shannon-greenlight/bonkulator/code/Bonkulator/trigger_fxns.h

// Trigger functions
#include "Arduino.h"

void clear_trigger(int output_num, int trig_num)
{
    OutputData *outptr = &outputs[output_num];
    (*bonk_outputs[output_num]).clear_trigger(trig_num);
    outptr->repeat_count = (*bonk_outputs[output_num]).get_param(OUTPUT_REPEAT);
    outptr->next_time = (*bonk_outputs[output_num]).get_param(OUTPUT_INIT_DELAY) + millis();
}

void clear_outputs(int trig_num)
{
    for (int output_num = 0; output_num < NUM_OUTPUTS; output_num++)
    {
        clear_trigger(output_num, trig_num);
    }
}

void select_trigger(int int_param)
{
    switch (int_param)
    {
    case 0:
        selected_trigger = &trig0;
        break;
    case 1:
        selected_trigger = &trig1;
        break;
    case 2:
        selected_trigger = &trig2;
        break;
    case 3:
        selected_trigger = &trig3;
        break;
    }
    if (in_output_fxn())
    {
        selected_fxn->put_param_num(selected_trigger->trig_num + OUTPUT_ENABLE_T0);
    }
    else
    {
        selected_fxn->put_param_num(selected_trigger->trig_num + BOUNCE_ENABLE_T0);
    }
    // selected_fxn->printParams();
}

void clear_all_triggers()
{
    int trigger_save = selected_trigger->trig_num;
    for (int i = 0; i < NUM_TRIGGERS; i++)
    {
        clear_outputs(i);
        // select_trigger(i);
        (*triggers[i]).clear();
    }
    select_trigger(trigger_save);
}

bool check_any_triggers()
{
    bool triggered = false;
    for (int i = 0; i < NUM_TRIGGERS; i++)
    {
        if ((*triggers[i]).state == TRIGGER_ACTIVE)
        {
            triggered = true;
            // (*triggers[i]).state = TRIGGER_IDLE;
            (*triggers[i]).clear();
        }
    }
    return triggered;
}

String check_output_triggers()
{
    String out = "";
    String t = "     ";
    for (int i = 0; i < NUM_OUTPUTS; i++)
    {
        if ((*bonk_outputs[i]).get_param(OUTPUT_CLOCK) == 1)
        {
            t = " X" + String(bonk_output(i).triggered_by) + "  ";
        }
        else
        {
            t = "     ";
            if ((*bonk_outputs[i]).triggered)
            {
                t = " T" + String(bonk_output(i).triggered_by) + "  ";
            }
        }
        out += String(i) + ":" + t;
    }
    return out;
}

bool trigger_inactive(int trig_num)
{
    bool trigger_active = false;
    for (int i = 0; i < NUM_OUTPUTS; i++)
    {
        if ((*bonk_outputs[i]).get_param(OUTPUT_ENABLE_T0 + trig_num) && (*bonk_outputs[i]).triggered)
        {
            trigger_active = true;
        }
    }
    return !trigger_active;
}

void send_trig_status_to_USB()
{
    static trigger_state t0_memory;
    static trigger_state t1_memory;
    static trigger_state t2_memory;
    static trigger_state t3_memory;
    if (usb_direct_enabled())
    {
        if (trig0.state != t0_memory)
        {
            send_status_to_USB();
            t0_memory = trig0.state;
        }

        if (trig1.state != t1_memory)
        {
            send_status_to_USB();
            t1_memory = trig1.state;
        }

        if (trig2.state != t2_memory)
        {
            send_status_to_USB();
            t2_memory = trig2.state;
        }

        if (trig3.state != t3_memory)
        {
            send_status_to_USB();
            t3_memory = trig3.state;
        }
    }
}

void check_triggers()
{
    send_trig_status_to_USB();
    for (int trig_num = 0; trig_num < 4; trig_num++)
    {
        if (trigger_inactive(trig_num))
        {
            digitalWrite(trigger_leds[trig_num], LOW);
            (*triggers[trig_num]).state = TRIGGER_IDLE;
        }
    }
}

void trigger0()
{
    trig0.trigger();
}

void trigger1()
{
    trig1.trigger();
}

void trigger2()
{
    trig2.trigger();
}

void trigger3()
{
    trig3.trigger();
}

void trigger_output(byte trig_num, int output_num)
{
    OutputData *outptr = &outputs[output_num];
    (*bonk_outputs[output_num]).trigger(trig_num, (*bonk_outputs[output_num]).get_param(OUTPUT_REPEAT) == 0);
    if ((*bonk_outputs[output_num]).get_param(OUTPUT_CLOCK) != 1 && (*bonk_outputs[output_num]).get_param(OUTPUT_WAVEFORM) != WAVEFORM_TOGGLE)
    {
        outptr->current_index = 0;
        // digitalWrite(trigger_leds[3], output_num == 0 ? HIGH : LOW);
        outptr->repeat_count = (*bonk_outputs[output_num]).get_param(OUTPUT_REPEAT);
        outptr->next_time = (*bonk_outputs[output_num]).get_param(OUTPUT_INIT_DELAY) + millis();
    }
    // set led
    digitalWrite(trigger_leds[trig_num], HIGH);
}

void trigger_report()
{
    ui.t.clrDown("15");
    ui.terminal_printRow("Trigger Report", "16");
    Serial.println(F("Output\tT0\tT1\tT2\tT3\tTriggered"));
    ui.t.printChars(50, "-");
    Serial.print("\r\n");
    // Serial.println(F("----------------------------------"));
    for (int i = 0; i < NUM_OUTPUTS; i++)
    {
        Serial.print(String(i));
        Serial.print("\t");
        Serial.print(String((*bonk_outputs[i]).get_param(OUTPUT_ENABLE_T0)));
        Serial.print("\t");
        Serial.print(String((*bonk_outputs[i]).get_param(OUTPUT_ENABLE_T1)));
        Serial.print("\t");
        Serial.print(String((*bonk_outputs[i]).get_param(OUTPUT_ENABLE_T2)));
        Serial.print("\t");
        Serial.print(String((*bonk_outputs[i]).get_param(OUTPUT_ENABLE_T3)));
        Serial.print("\t");
        Serial.println(String((*bonk_outputs[i]).triggered));
    }
    Serial.println();
    Serial.println(F("Input\tT0\tT1\tT2\tT3"));
    ui.t.printChars(50, "-");
    Serial.print("\r\n");
    // Serial.println(F("----------------------------------"));
    for (int i = 0; i < NUM_INPUTS; i++)
    {
        Serial.print(String(i));
        Serial.print("\t");
        Serial.print(String((*bounce_fxns[i]).get_param(BOUNCE_ENABLE_T0)));
        Serial.print("\t");
        Serial.print(String((*bounce_fxns[i]).get_param(BOUNCE_ENABLE_T1)));
        Serial.print("\t");
        Serial.print(String((*bounce_fxns[i]).get_param(BOUNCE_ENABLE_T2)));
        Serial.print("\t");
        Serial.print(String((*bounce_fxns[i]).get_param(BOUNCE_ENABLE_T3)));
        Serial.println();
        // Serial.print("\t");
        // Serial.println(String((*bonk_outputs[i]).triggered));
    }
    Serial.println();
    Serial.println("Trigger Channels");
    ui.t.printChars(16, "-");
    Serial.println();
    for (int i = 0; i < NUM_TRIGGERS; i++)
    {
        (*triggers[i]).trigger_report();
    }
}

void triggers_begin()
{
    attachInterrupt(digitalPinToInterrupt(T0_PIN), trigger0, RISING);
    attachInterrupt(digitalPinToInterrupt(T1_PIN), trigger1, RISING);
    attachInterrupt(digitalPinToInterrupt(T2_PIN), trigger2, RISING);
    attachInterrupt(digitalPinToInterrupt(T3_PIN), trigger3, RISING);
}
